maxhuangPENN/CBE3300-project-page/fuelcellinformationflow.jpg

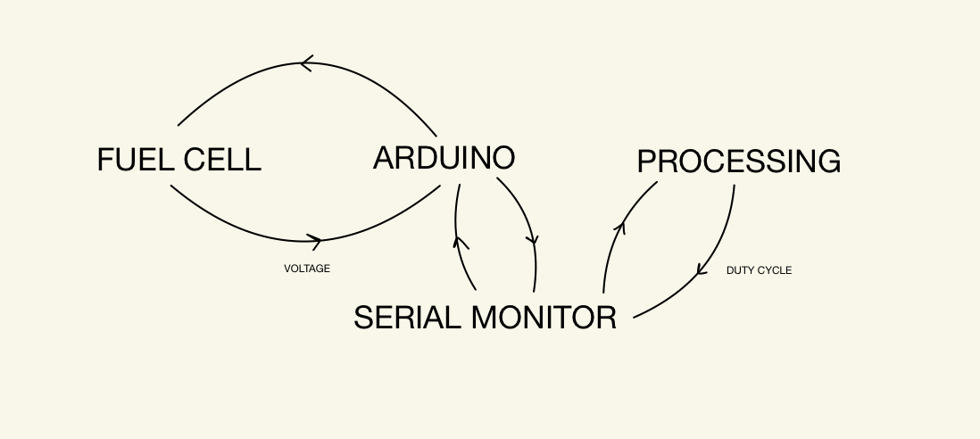
fuelcellinformationflow.jpg
