maxhuangPENN/CBE3300-project-page/membrane-image.png

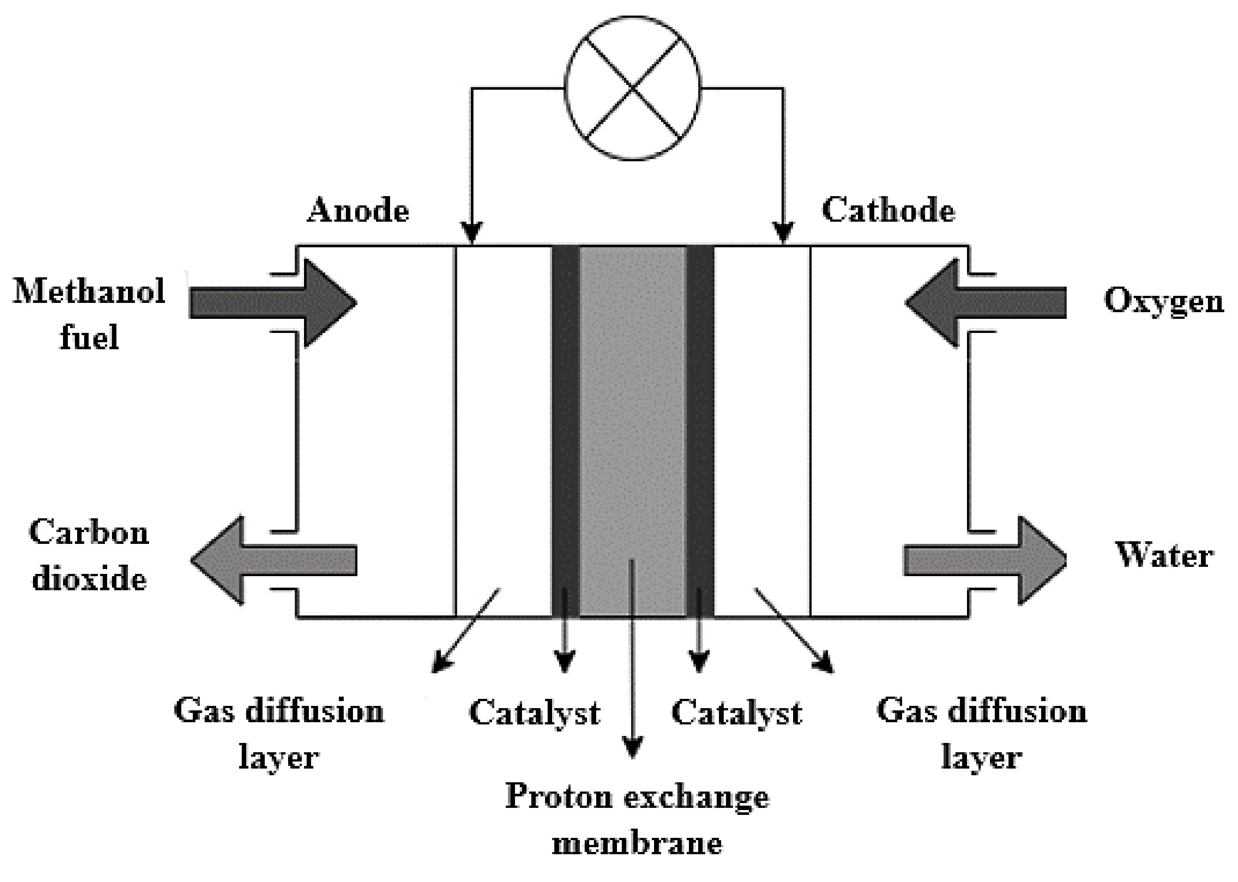
membrane-image.png
