maxhuangPENN/CBE3300-project-page/updatedcircuitdiagram.jpg

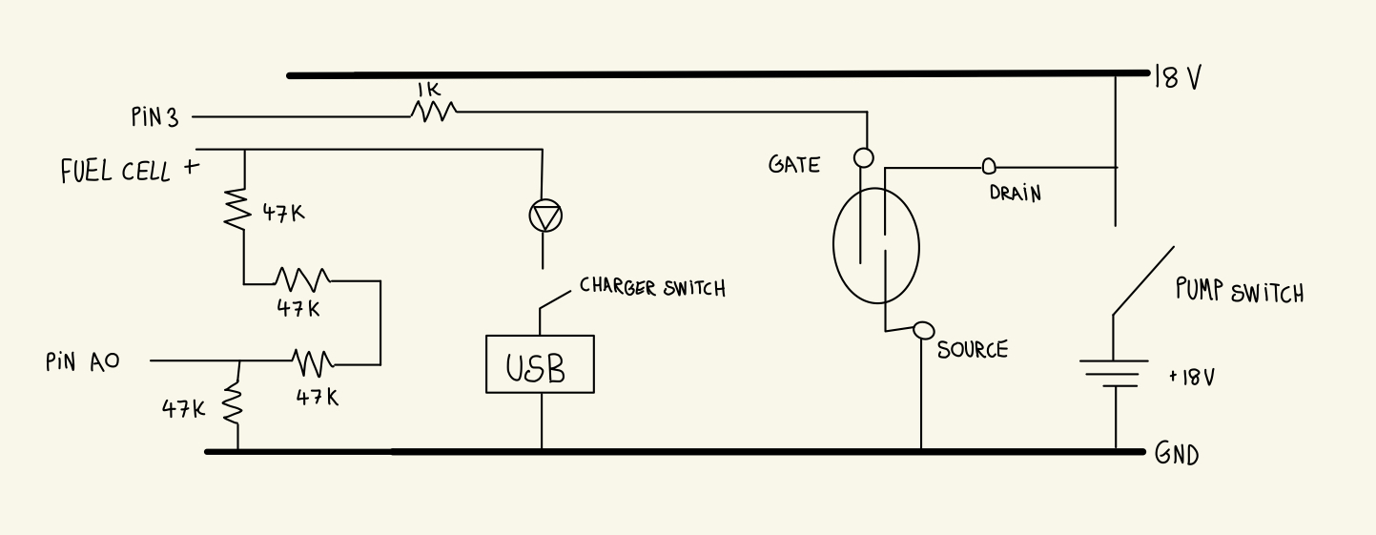
updatedcircuitdiagram.jpg
