maxhuangPENN/CBE3300-project-page/calibration curve.png

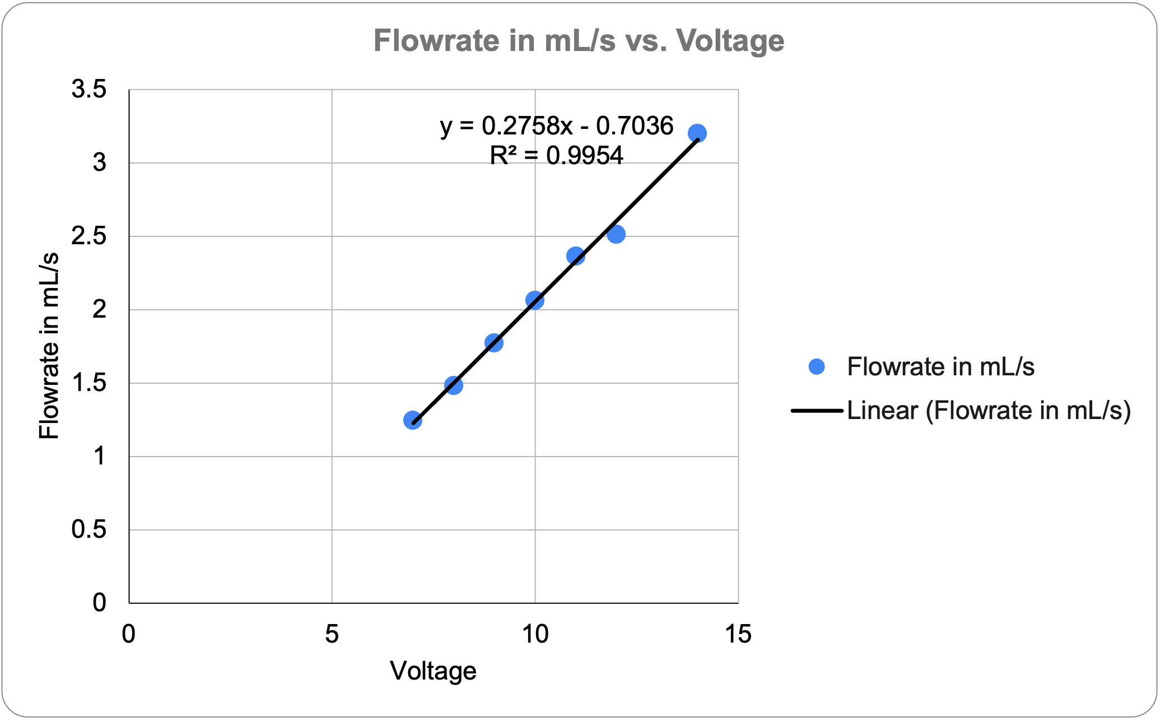
calibration curve.png
