maxhuangPENN/CBE3300-project-page/DMFCCodeWorkingFeedback.pde

import processing.serial.*;
import java.io.PrintWriter;

Serial myPort;
ArrayList<Float> voltageData = new ArrayList<Float>();
ArrayList<String> timeData = new ArrayList<String>();

PrintWriter output;
boolean isRunning = true;
int maxPoints = 300;
float minV = 0;
float maxV = 6;

// User controls
Button toggleButton;
TextField inputField;
Button sendButton;

// Battery & control parameters
float batteryCapacity_mAh = 20000;
float batteryVoltage = 3.7;
float efficiency = 0.3f;

// Feedback control
float dutyCycle = 0.5;
float riemannCounter = 0;
float lastVoltage = 0;
int lastFeedbackTime = 0;
int feedbackInterval = 60000;

float targetVoltage = 5;

void setup() {
  size(900, 600);
  println(Serial.list());
  String portName = Serial.list()[0];
  myPort = new Serial(this, portName, 9600);
  myPort.bufferUntil('\n');

  String timestamp = year() + nf(month(), 2) + nf(day(), 2) + "_" + nf(hour(), 2) + nf(minute(), 2);
  output = createWriter("voltage_log_" + timestamp + ".csv");
  output.println("Time (s),Voltage (V)");

  toggleButton = new Button("Pause", width - 120, 20, 80, 30);
  sendButton = new Button("Set Time (days)", 400, 550, 140, 30);
  inputField = new TextField(250, 550, 130, 30);
}

void draw() {
  background(255);
  drawAxes();
  drawPlot();
  drawLabels();
  toggleButton.display();
  sendButton.display();
  inputField.display();

  feedbackControl();
}

void serialEvent(Serial p) {
  if (!isRunning) return;

  String input = p.readStringUntil('\n');
  if (input != null) {
    input = trim(input);
    try {
      float voltage = float(input);
      voltageData.add(voltage);
      timeData.add(str(millis() / 1000.0));

      if (voltageData.size() > maxPoints) {
        voltageData.remove(0);
        timeData.remove(0);
      }

      output.println(timeData.get(timeData.size() - 1) + "," + voltage);
    } catch (Exception e) {
      println("Parse error: " + input);
    }
  }
}

void feedbackControl() {
  if (millis() - lastFeedbackTime >= feedbackInterval && voltageData.size() >= 2) {
    lastFeedbackTime = millis();

    float currentVoltage = voltageData.get(voltageData.size() - 1);
    float previousVoltage = voltageData.get(voltageData.size() - 2);
    float deltaV = currentVoltage - previousVoltage;
    float voltageError = targetVoltage - currentVoltage;
    float updateMargin = 0.01;

    if (deltaV > -0.1 && deltaV < 0.1) {
      if (voltageError > 0.1) {
        dutyCycle = constrain(dutyCycle + updateMargin, 0.0, 1.0);
        riemannCounter -= voltageError;
      } else if (voltageError < -0.1) {
        dutyCycle = constrain(dutyCycle - updateMargin, 0.0, 1.0);
        riemannCounter += voltageError;
      } else if (riemannCounter > 1) {
        dutyCycle = constrain(dutyCycle - updateMargin, 0.0, 1.0);
      } else if (riemannCounter < -1) {
        dutyCycle = constrain(dutyCycle + updateMargin, 0.0, 1.0);
      }
    } else {
      riemannCounter -= voltageError;
    }

    myPort.write("SET:" + dutyCycle + "\n");
    println("Feedback Updated — Duty Cycle: " + nf(dutyCycle, 1, 2) + ", Riemann: " + nf(riemannCounter, 1, 2));
  }
}

void mousePressed() {
  if (toggleButton.isClicked(mouseX, mouseY)) {
    isRunning = !isRunning;
    toggleButton.label = isRunning ? "Pause" : "Start";
  }

  if (sendButton.isClicked(mouseX, mouseY)) {
    try {
      float days = float(inputField.text);
      float time = days * 24;
      float K = 4.5 / 8.62;
      // Constants
      float C = 10;
      float Rthev = 72.5;
      float threshold = 5.4;
      float targetVoltage = threshold + C * Rthev / time;
      float voltageToPump = (targetVoltage) / K;
      float newDuty = constrain(voltageToPump / 18.0, 0.0, 1.0);

      dutyCycle = newDuty;
      myPort.write("SET:" + dutyCycle + "\n");

      println("Charge Time (days): " + days);
      println("Target Voltage: " + targetVoltage);
      println("Voltage to Pump: " + voltageToPump + " V");
      println("Duty Cycle Sent: " + dutyCycle);
    } catch (Exception e) {
      println("Invalid input.");
    }
  }
}

void drawAxes() {
  stroke(0);
  line(60, 40, 60, height - 80);
  line(60, height - 80, width - 40, height - 80);
}

void drawPlot() {
  noFill();
  stroke(50, 100, 255);
  beginShape();
  for (int i = 0; i < voltageData.size(); i++) {
    float x = map(i, 0, maxPoints, 60, width - 40);
    float y = map(voltageData.get(i), minV, maxV, height - 80, 40);
    vertex(x, y);
  }
  endShape();

  // Target line
  float yTarget = map(targetVoltage, minV, maxV, height - 80, 40);
  stroke(200, 0, 0);
  line(60, yTarget, width - 40, yTarget);
  fill(200, 0, 0);
  //text("Target: " + nf(targetVoltage, 1, 2) + " V", width - 150, yTarget - 5);
}

void drawLabels() {
  fill(0);
  textSize(14);
  text("Live Voltage (V)", 20, 20);
  textAlign(CENTER);
  text("Time (rolling)", width / 2, height - 40);

  for (float v = minV; v <= maxV; v += 1) {
    float y = map(v, minV, maxV, height - 80, 40);
    textAlign(RIGHT);
    text(nf(v, 1, 1), 55, y + 5);
    stroke(230);
    line(60, y, width - 40, y);
  }
}

void exit() {
  output.flush();
  output.close();
  super.exit();
}

class Button {
  String label;
  int x, y, w, h;

  Button(String label, int x, int y, int w, int h) {
    this.label = label;
    this.x = x;
    this.y = y;
    this.w = w;
    this.h = h;
  }

  void display() {
    fill(240);
    stroke(0);
    rect(x, y, w, h, 5);
    fill(0);
    textAlign(CENTER, CENTER);
    text(label, x + w / 2, y + h / 2);
  }

  boolean isClicked(int mx, int my) {
    return mx > x && mx < x + w && my > y && my < y + h;
  }
}

class TextField {
  int x, y, w, h;
  String text = "";

  TextField(int x, int y, int w, int h) {
    this.x = x;
    this.y = y;
    this.w = w;
    this.h = h;
  }

  void display() {
    fill(255);
    stroke(0);
    rect(x, y, w, h);
    fill(0);
    textAlign(LEFT, CENTER);
    text(text, x + 5, y + h / 2);
  }

  void keyPressed() {
    if (key == BACKSPACE && text.length() > 0) {
      text = text.substring(0, text.length() - 1);
    } else if (key >= 32 && key <= 126) {
      text += key;
    }
  }
}

void keyPressed() {
  inputField.keyPressed();
}
